david-beaudette/stan-base/test/test_lcd/test_lcd.c

/** STAN THE STANDING ROBOT
   Program to test the LCD2004 module interface
   by David Beaudette
**/

// Libraries
#include <stdio.h>

#include "pico/stdlib.h"
#include "lcd.h"
#include "uip.h"

int main() {
  const uint LED_PIN = PICO_DEFAULT_LED_PIN;
  bool led_state_b = true;
  float pot_pct_f32 = 0.0f;
  char pot_str[20];

  gpio_init(LED_PIN);
  gpio_set_dir(LED_PIN, GPIO_OUT);
  stdio_init_all();

  uip_init();

  // Initialise sensor in accelerometer only mode
  while (!lcd_init()) {
    printf("LCD init failed, retrying in 2 s\n");
    sleep_ms(2000);
  }

  lcd_home();
  lcd_print("LCD Test: Turn Pot");
  sleep_ms(2000);

  // Infinite Loop
  while (1) {
    gpio_put(LED_PIN, led_state_b);
    led_state_b = !led_state_b;

    pot_pct_f32 = uip_get_pot_pct();

    lcd_setCursor(1, 0);
    sprintf(pot_str, "Pot pos: %6.2f%%", pot_pct_f32);
    lcd_print(pot_str);
    printf("%s\n", pot_str);
    sleep_ms(500);
  }

  return 0;
}
