david-beaudette/stan-base/test/test_mtr_pot/test_mtr_pot.c

/** STAN THE STANDING ROBOT
   Program to test the motor control function
   by David Beaudette
**/

// Libraries
#include <stdio.h>
#include "pico/stdlib.h"

#include "hardware/clocks.h"
#include "hardware/pwm.h"

#include "mtr.h"
#include "uip.h"
#include "uti.h"

#define RAMP_DELAY_MS 10
#define FIXPOS_DELAY_MS 250
#define NUM_SPEED_VALUES 5
// #define TEST_LIMITS

int main() {
  const uint LED_PIN = PICO_DEFAULT_LED_PIN;
  gpio_init(LED_PIN);
  gpio_set_dir(LED_PIN, GPIO_OUT);

  stdio_init_all();

  sleep_ms(500);

  mtr_init();
  uip_init();

  mtr_enable();
  printf("Motors are enabled.\n");

  printf("Slice   L %d  R %d\n", pwm_gpio_to_slice_num(MTR_STEP_L_PIN),
                                 pwm_gpio_to_slice_num(MTR_STEP_R_PIN));
  printf("Channel L %d  R %d\n", pwm_gpio_to_channel(MTR_STEP_L_PIN),
                                 pwm_gpio_to_channel(MTR_STEP_R_PIN));

  float speed_left_cur_f32 = 0.0f;
  float speed_right_cur_f32 = 0.0f;
  float pot_angle_f32 = 0.0f;
  bool led_state_b = true;
  int speed_idx = 0;

  while (true) {    
    gpio_put(LED_PIN, led_state_b);
    led_state_b = !led_state_b;

    pot_angle_f32 = uip_get_pot_pct();

    speed_left_cur_f32 = mtr_set_speed(
        MTR_LEFT, map(pot_angle_f32, 0.0f, 100.0f, -50.0f, 50.0f));
    speed_right_cur_f32 =
        mtr_set_speed(MTR_RIGHT, speed_left_cur_f32);

    sleep_ms(100);
    printf("Speed left: %f (count %lld); right: %f (count %lld)\n",
           speed_left_cur_f32, 
           mtr_get_left_count(),
           speed_right_cur_f32,
           mtr_get_right_count());

    ++speed_idx;
    if(speed_idx == NUM_SPEED_VALUES) {
      speed_idx = 0;
    }
  }
  printf("Stepper motor test complete.\n");
  mtr_disable();

  return 0;
}
